JaviElio/Christmas-Ornaments/Images/Text2.bmp

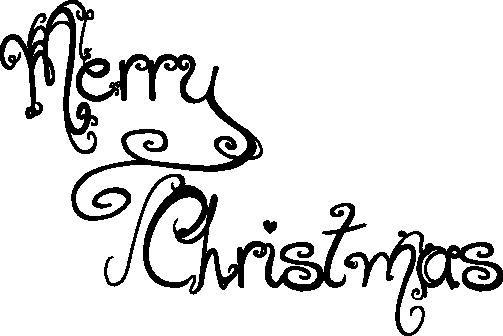
Images/Text2.bmp
