JaviElio/Christmas-Ornaments/Images/Text.bmp

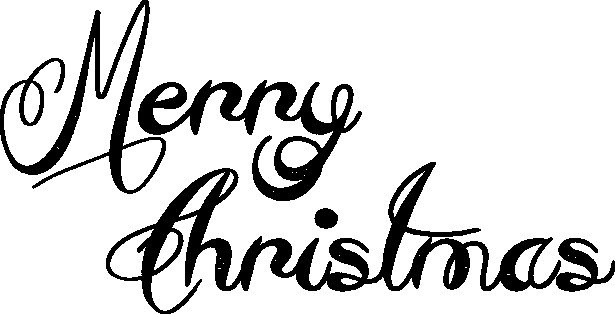
Images/Text.bmp
