JaviElio/Christmas-Ornaments/Images/Tree_Shadow.bmp

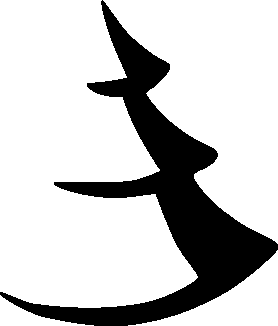
Images/Tree_Shadow.bmp
